G1OJS/ATTiny85-Scanner-Radio/dev/LtSpice Analysis/IF Amp with MC1350 from Schematic.asc

C1: cap; 10p
C2: cap; 100p
C3: cap; 1µ
C4: cap; 150p
C5: cap; 10n
C6: cap; 100p
C7: cap; 10n
C8: cap; 33p
C9: cap; 1µ
C12: cap; 10n
C13: cap; 39p
C14: cap; 1µ
J1: njf; 2N3819
L1: ind; 4.7µH
L2: ind; 4.7µH
R1: res; 100k
R2: res; 33k
R3: res; 5.1k
R4: res; 1000k
R5: res; 1
R6: res; 820
R7: res; 1
R8: res; 820
R9: res; 5.1k
R10: res; 820
V1: voltage; {Vagc}
V7: voltage; 5
V8: voltage; ""; AC 0.00035566; Rser=1500
X1: 
X2: 
X3: 
X5: 
Named nets: 0, Y2load, Y1load, Stage1-out, Stage1-in, Stage2-out
.ac lin 251 10650000 10750000
.param Vagc=2.7
