G1OJS/ATTiny85-Scanner-Radio/LtSpice/MC1350/MC1350_from_schematic.asc

D1: diode
D2: diode
D3: diode
D4: diode
Q1: npn; 2N3904
Q2: npn; 2N3904
Q3: npn; 2N3904
Q4: npn; 2N3904
Q5: npn; 2N3904
Q6: npn; 2N3904
Q7: npn; 2N3904
Q8: npn; 2N3904
Q9: npn; 2N3904
Q10: npn; 2N3904
Q11: npn; 2N3904
Q12: npn; 2N3904
Q13: npn; 2N3904
Q14: npn; 2N3904
Q15: npn; 2N3904
Q17: npn; 2N3904
R1: res; 1
R2: res; 1.1k
R3: res; 1.1k
R4: res; 66
R5: res; 5k
R6: res; 5k
R7: res; 470
R8: res; 2k
R9: res; 470
R10: res; 70
R11: res; 1.47k
R12: res; 5.3k
R13: res; 8.4k
R14: res; 1.4k
R15: res; 5.6k
R16: res; 12.1k
R17: res; 1.9k
R18: res; 45
R19: res; 200
R20: res; 200
R21: res; 2.8k
R22: res; 2.8k
R23: res; 200
Named nets: 6, 7, 4, 5, 2, 8, 1, 3
