G1OJS/ATTiny85-Scanner-Radio/dev/LtSpice Analysis/Infinite Impedance Detector.asc

C1: cap; 10n
C2: cap; .1µ
C3: cap; 100p
J1: njf
R1: res; 33k
R2: res; 100k
R3: res; 1k
V1: voltage; 5
X2: 
Named nets: 0
.tran 10m
