G1OJS/ATTiny85-Scanner-Radio/dev/LtSpice Analysis/LO Filter.asc

C1: cap; 3p
C3: cap; 3pF; Rser=1
L1: ind; 4.7µH; Rser=1
R2: res; 1500
V2: voltage; PULSE(0 3 0 0 0 {0.5/(MHz*1e6)} {1/(MHz*1e6)}); Rser=85
Named nets: 0
.tran 0 10us 9.9us
.param MHz=130
