G1OJS/ATTiny85-Scanner-Radio/dev/LtSpice Analysis/RF input amp.asc

C1: cap; 3p
C4: cap; 10p
C5: cap; 30p
L1: ind; .1µH
Q2: npn; 2SC3355
R6: res; 560
R7: res; 100k
R8: res; 1500
R10: res; 50
V3: voltage; ""; AC .0001
V4: voltage; 5
Named nets: 0, o2, i2
.ac lin 51 118000000 136000000
.lib C:\\Users\\drala\\Documents\\Projects\\LtSpiceLibs\\local.bjt
