G1OJS/ATTiny85-Scanner-Radio/LtSpice/LT10.7MFP/Ceramic_Filter_v1_10704_kHz_600_Ohms.asc

C1: cap; .033pF
C2: cap; .033pF
C6: cap; 9.378nF
L1: ind; 6.7mH
L2: ind; 6.7mH
L3: ind; 23.59nH
Named nets: 1, 2, 3
.param Cs=3pF
.param L=1.55uH
.param Cp=141pF
